ok1cdj/OpenCWKeyerMK2/images/opencwkeyermk2-arduino-header.jpg

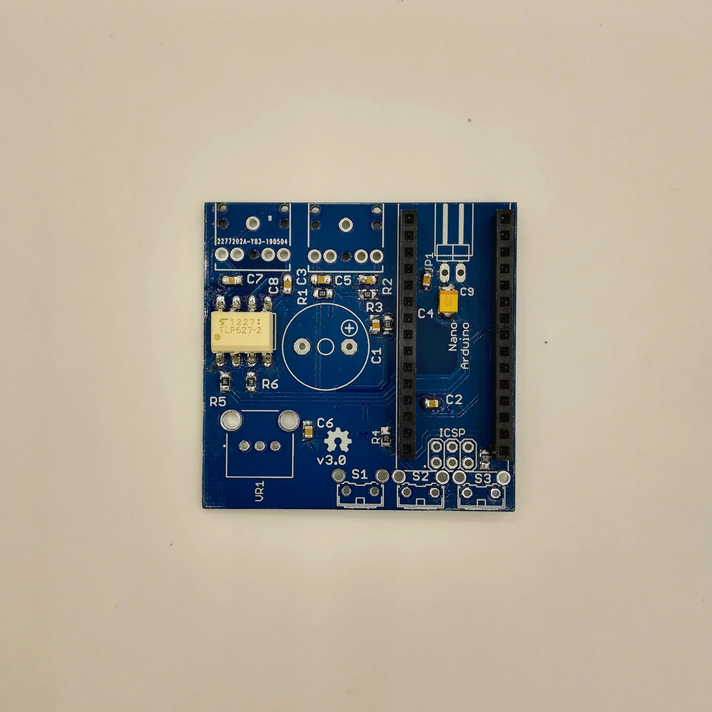
images/opencwkeyermk2-arduino-header.jpg
