ok1cdj/OpenCWKeyerMK2/images/opencwkeyermk2-arduino.jpg

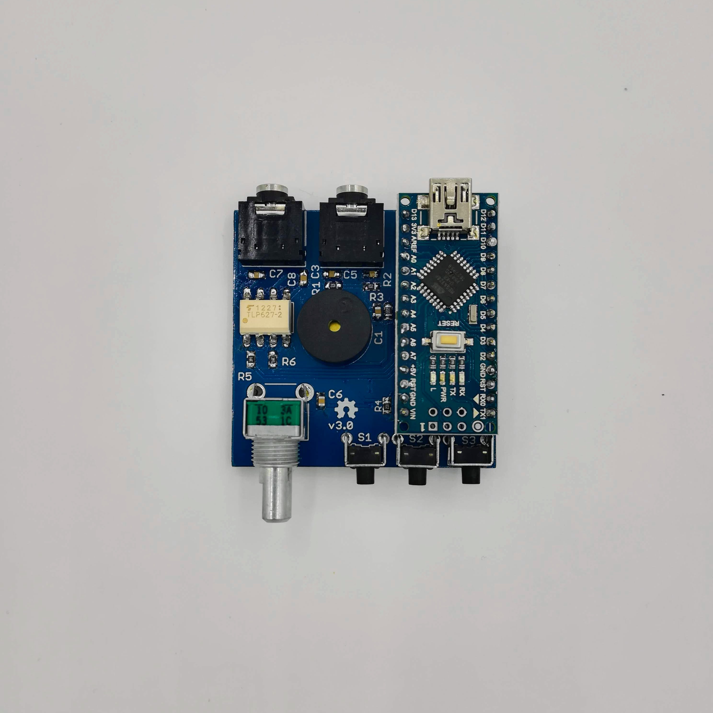
images/opencwkeyermk2-arduino.jpg
