ok1cdj/OpenCWKeyerMK2/images/opencwkeyermk2-connectors.jpg

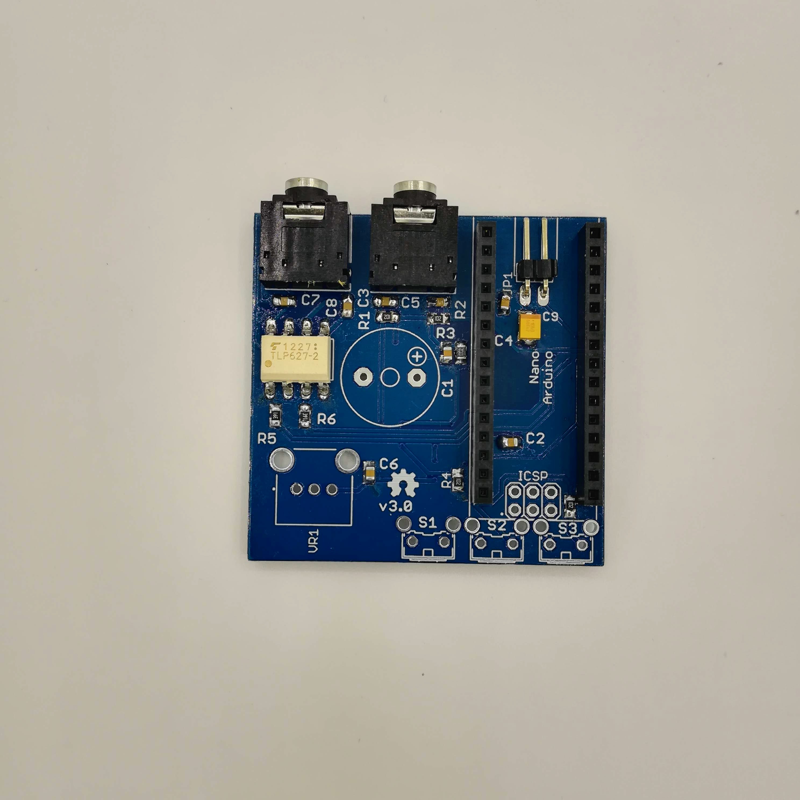
images/opencwkeyermk2-connectors.jpg
