ok1cdj/OpenCWKeyerMK2/images/opencwkeyermk2-switches.jpg

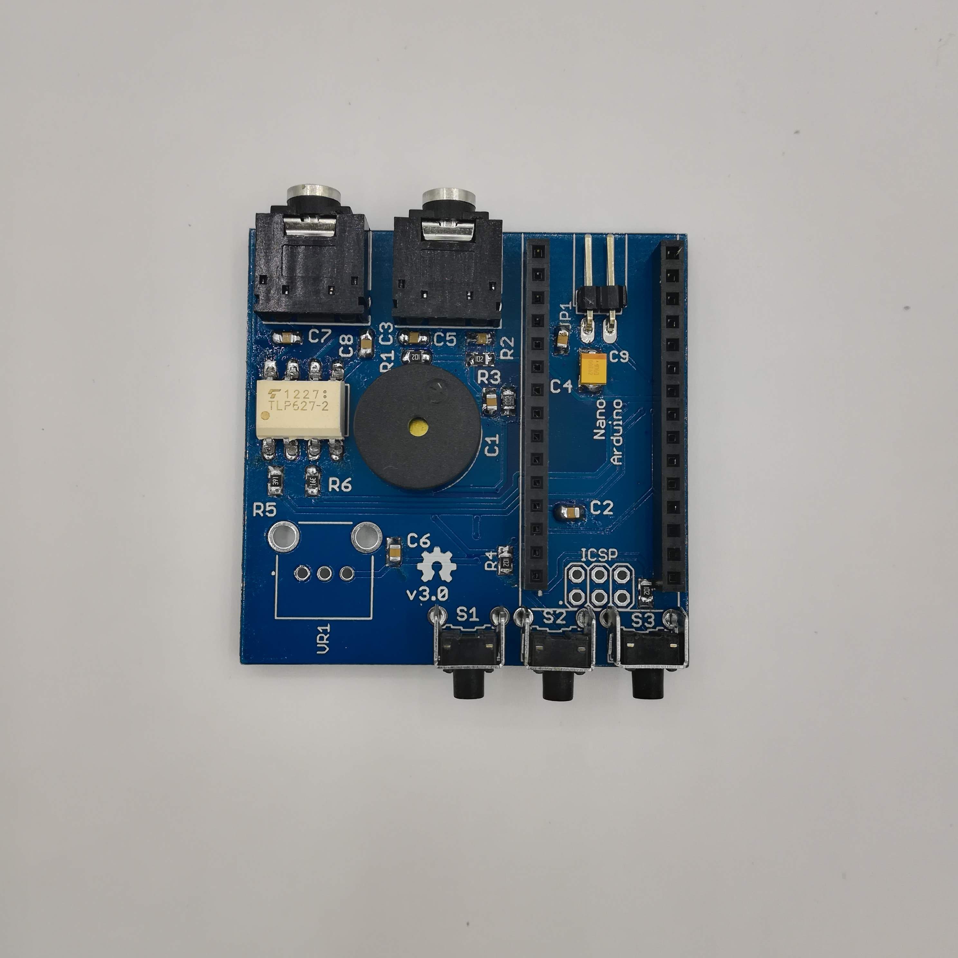
images/opencwkeyermk2-switches.jpg
