ok1cdj/OpenCWKeyerMK2/open_cw_keyer_mk2_v30-top.png

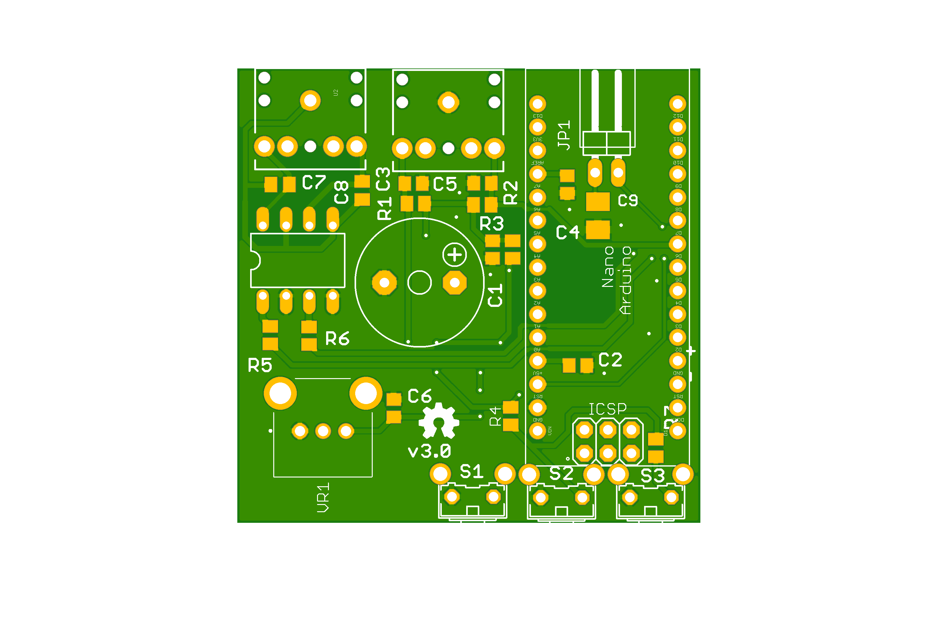
open_cw_keyer_mk2_v30-top.png
